roc-ket-cod-er/Cpeedo-mk5/Firmware/ESP32/sample_secrets.py

key = "YOUR ADAFRUIT IO KEY"
user_name = "YOUR ADAFRUIT IO USER NAME"
client_id = "A NAME FOR YOUR DEVICE"

# If you have wifi, fill out the following. If not, delete the dictionary.

wifi_info = {
    "YOUR SSID": "YOUR PASSWORD",
    "YOUR 2nd SSID": "ITS PASSOWRD"
}
